denisbohm/firefly-snowflake/firmware/src/fd_breathe_animation.c

#include "fd_breathe_animation.h"

const uint32_t fd_breathe_grbzs[] = {
 0x00000000, 0x00000000, 0x00000000, 0x00130000, 0x00400000, 0x00200000, 0x00000000, 0x00000000, 0x00000000, 0x00000000, 0x00000000, 0x00130000, 0x00000000,
 0x00000000, 0x00000000, 0x00000000, 0x00190000, 0x00360000, 0x001f0000, 0x00000000, 0x00000000, 0x00000000, 0x00000000, 0x00000000, 0x000c0000, 0x00000000,
 0x00000000, 0x00000000, 0x00020000, 0x00200000, 0x002c0000, 0x001d0000, 0x00000000, 0x00000000, 0x00000000, 0x00000000, 0x00000000, 0x00050000, 0x00000000,
 0x00000000, 0x00000000, 0x00070000, 0x00260000, 0x00220000, 0x001a0000, 0x00000000, 0x00000000, 0x00000000, 0x00000000, 0x00000000, 0x00000000, 0x00000000,
 0x00060000, 0x00000000, 0x000c0000, 0x002a0000, 0x00180000, 0x00150000, 0x00000000, 0x00000000, 0x00000000, 0x00000000, 0x00000000, 0x00000000, 0x00000000,
 0x000f0000, 0x00000000, 0x00110000, 0x002c0000, 0x000f0000, 0x00110000, 0x00000000, 0x00000000, 0x00000000, 0x00000000, 0x00000000, 0x00000000, 0x00000000,
 0x00180000, 0x00000000, 0x00150000, 0x002a0000, 0x00060000, 0x000c0000, 0x00000000, 0x00000000, 0x00000000, 0x00000000, 0x00000000, 0x00000000, 0x00000000,
 0x00220000, 0x00000000, 0x001a0000, 0x00260000, 0x00000000, 0x00070000, 0x00000000, 0x00000000, 0x00000000, 0x00000000, 0x00000000, 0x00000000, 0x00000000,
 0x002c0000, 0x00050000, 0x001d0000, 0x00200000, 0x00000000, 0x00020000, 0x00000000, 0x00000000, 0x00000000, 0x00000000, 0x00000000, 0x00000000, 0x00000000,
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
 0x00000000, 0x00000000, 0x00000000, 0x00000000, 0x00180000, 0x00150000, 0x00000000, 0x00000000, 0x00000000, 0x00000000, 0x000c0000, 0x002a0000, 0x00060000,
 0x00000000, 0x00000000, 0x00000000, 0x00000000, 0x00220000, 0x001a0000, 0x00000000, 0x00000000, 0x00000000, 0x00000000, 0x00070000, 0x00260000, 0x00000000,
 0x00000000, 0x00000000, 0x00000000, 0x00050000, 0x002c0000, 0x001d0000, 0x00000000, 0x00000000, 0x00000000, 0x00000000, 0x00020000, 0x00200000, 0x00000000,
 0x00000000, 0x00000000, 0x00000000, 0x00000000, 0x00000000, 0x00000000, 0x00000000, 0x00000000, 0x00000000, 0x00000000, 0x00000000, 0x00000000, 0x00000000,
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
};

const uint8_t fd_breathe_instructions[] = {
    fd_snowflake_operation_illuminate, fd_snowflake_operand(40), fd_snowflake_operand(40 * 13 * 0),
    fd_snowflake_operation_sleep, fd_snowflake_operand(58),
    fd_snowflake_operation_illuminate, fd_snowflake_operand(40), fd_snowflake_operand(40 * 13 * 1),
    fd_snowflake_operation_sleep, fd_snowflake_operand(58),
    fd_snowflake_operation_illuminate, fd_snowflake_operand(40), fd_snowflake_operand(40 * 13 * 2),
    fd_snowflake_operation_sleep, fd_snowflake_operand(58),
    fd_snowflake_operation_illuminate, fd_snowflake_operand(40), fd_snowflake_operand(40 * 13 * 3),
    fd_snowflake_operation_sleep, fd_snowflake_operand(58),
    fd_snowflake_operation_illuminate, fd_snowflake_operand(40), fd_snowflake_operand(40 * 13 * 4),
    fd_snowflake_operation_sleep, fd_snowflake_operand(58),
    fd_snowflake_operation_illuminate, fd_snowflake_operand(40), fd_snowflake_operand(40 * 13 * 5),
    fd_snowflake_operation_sleep, fd_snowflake_operand(58),
    fd_snowflake_operation_illuminate, fd_snowflake_operand(40), fd_snowflake_operand(40 * 13 * 6),
    fd_snowflake_operation_sleep, fd_snowflake_operand(58),
    fd_snowflake_operation_illuminate, fd_snowflake_operand(40), fd_snowflake_operand(40 * 13 * 7),
    fd_snowflake_operation_sleep, fd_snowflake_operand(58),
    fd_snowflake_operation_illuminate, fd_snowflake_operand(40), fd_snowflake_operand(40 * 13 * 8),
    fd_snowflake_operation_sleep, fd_snowflake_operand(58),
    fd_snowflake_operation_illuminate, fd_snowflake_operand(40), fd_snowflake_operand(40 * 13 * 9),
    fd_snowflake_operation_sleep, fd_snowflake_operand(58),
    fd_snowflake_operation_restart,
};

const fd_snowflake_program_t fd_breathe_program = {
    .instructions = fd_breathe_instructions,
    .grbzs = fd_breathe_grbzs,
};
